schef/midi-organ/arduino/tests/deadcat/serial/74hc595-6/knight_rider_6.ino

//**************************************************************//
//  Name    : shiftOutCode, Hello World                                
//  Author  : Carlyn Maw,Tom Igoe, David A. Mellis 
//  Date    : 25 Oct, 2006    
//  Modified: 23 Mar 2010                                 
//  Version : 2.0                                             
//  Notes   : Code for using a 74HC595 Shift Register           //
//          : to count from 0 to 255                           
// http://arduino.cc/en/tutorial/ShiftOut
//****************************************************************

//Pin connected to ST_CP of 74HC595
int latchPin = 9; //SS
//Pin connected to SH_CP of 74HC595
int clockPin = 13; //SCK
////Pin connected to DS of 74HC595
int dataPin = 11; //MOSI

int oneByOne[8] = {1, 2, 4, 8, 16, 32, 64, 128};

int potPin = 5;    // select the input pin for the potentiometer

void setup() {
	//set pins to output so you can control the shift register
	pinMode(latchPin, OUTPUT);
	pinMode(clockPin, OUTPUT);
	pinMode(dataPin, OUTPUT);
}

int timer = 0;

void loop() {
	timer = analogRead(potPin);    // read the value from the sensor

	// count from 0 to 255 and display the number 
	// on the LEDs
	for (int i = 0; i < 8; i++) {
		// take the latchPin low so 
		// the LEDs don't change while you're sending in bits:
		digitalWrite(latchPin, LOW);
		// shift out the bits:
		shiftOut(dataPin, clockPin, MSBFIRST, 0);  
		shiftOut(dataPin, clockPin, MSBFIRST, 0);  
		shiftOut(dataPin, clockPin, MSBFIRST, 0);  
		shiftOut(dataPin, clockPin, MSBFIRST, 0);  
		shiftOut(dataPin, clockPin, MSBFIRST, 0);  
		shiftOut(dataPin, clockPin, MSBFIRST, oneByOne[i]);  

		//take the latch pin high so the LEDs will light up:
		digitalWrite(latchPin, HIGH);
		// pause before next value:
		timer = analogRead(potPin);    // read the value from the sensor
		delay(timer);
	}
	for (int i = 0; i < 8; i++) {
		// take the latchPin low so 
		// the LEDs don't change while you're sending in bits:
		digitalWrite(latchPin, LOW);
		// shift out the bits:
		shiftOut(dataPin, clockPin, MSBFIRST, 0);  
		shiftOut(dataPin, clockPin, MSBFIRST, 0);  
		shiftOut(dataPin, clockPin, MSBFIRST, 0);  
		shiftOut(dataPin, clockPin, MSBFIRST, 0);  
		shiftOut(dataPin, clockPin, MSBFIRST, oneByOne[i]);  
		shiftOut(dataPin, clockPin, MSBFIRST, 0);  

		//take the latch pin high so the LEDs will light up:
		digitalWrite(latchPin, HIGH);
		// pause before next value:
		timer = analogRead(potPin);    // read the value from the sensor
		delay(timer);
	}
	for (int i = 0; i < 8; i++) {
		// take the latchPin low so 
		// the LEDs don't change while you're sending in bits:
		digitalWrite(latchPin, LOW);
		// shift out the bits:
		shiftOut(dataPin, clockPin, MSBFIRST, 0);  
		shiftOut(dataPin, clockPin, MSBFIRST, 0);  
		shiftOut(dataPin, clockPin, MSBFIRST, 0);  
		shiftOut(dataPin, clockPin, MSBFIRST, oneByOne[i]);  
		shiftOut(dataPin, clockPin, MSBFIRST, 0);  
		shiftOut(dataPin, clockPin, MSBFIRST, 0);  

		//take the latch pin high so the LEDs will light up:
		digitalWrite(latchPin, HIGH);
		// pause before next value:
		timer = analogRead(potPin);    // read the value from the sensor
		delay(timer);
	}
	for (int i = 0; i < 8; i++) {
		// take the latchPin low so 
		// the LEDs don't change while you're sending in bits:
		digitalWrite(latchPin, LOW);
		// shift out the bits:
		shiftOut(dataPin, clockPin, MSBFIRST, 0);  
		shiftOut(dataPin, clockPin, MSBFIRST, 0);  
		shiftOut(dataPin, clockPin, MSBFIRST, oneByOne[i]);  
		shiftOut(dataPin, clockPin, MSBFIRST, 0);  
		shiftOut(dataPin, clockPin, MSBFIRST, 0);  
		shiftOut(dataPin, clockPin, MSBFIRST, 0);  

		//take the latch pin high so the LEDs will light up:
		digitalWrite(latchPin, HIGH);
		// pause before next value:
		timer = analogRead(potPin);    // read the value from the sensor
		delay(timer);
	}
	for (int i = 0; i < 8; i++) {
		// take the latchPin low so 
		// the LEDs don't change while you're sending in bits:
		digitalWrite(latchPin, LOW);
		// shift out the bits:
		shiftOut(dataPin, clockPin, MSBFIRST, 0);  
		shiftOut(dataPin, clockPin, MSBFIRST, oneByOne[i]);  
		shiftOut(dataPin, clockPin, MSBFIRST, 0);  
		shiftOut(dataPin, clockPin, MSBFIRST, 0);  
		shiftOut(dataPin, clockPin, MSBFIRST, 0);  
		shiftOut(dataPin, clockPin, MSBFIRST, 0);  

		//take the latch pin high so the LEDs will light up:
		digitalWrite(latchPin, HIGH);
		// pause before next value:
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
	shiftOut(dataPin, clockPin, MSBFIRST, 0);  
	shiftOut(dataPin, clockPin, MSBFIRST, 0);  
	shiftOut(dataPin, clockPin, MSBFIRST, 0);  
	shiftOut(dataPin, clockPin, MSBFIRST, 0);  
	digitalWrite(latchPin, HIGH);
	timer = analogRead(potPin);    // read the value from the sensor
	delay(timer*3);

}
