schef/midi-organ/arduino/tests/deadcat/midi-recive-60/src/sketch.ino

/*Receive MIDI and check if note = 60
By Amanda Ghassaei
July 2012
http://www.instructables.com/id/Send-and-Receive-MIDI-with-Arduino/

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
*/

byte commandByte;
byte noteByte;
byte velocityByte;

byte noteOn = 144;

//light up led at pin 13 when receiving noteON message with note = 60

void setup(){
  Serial.begin(31250);
  pinMode(13,OUTPUT);
  digitalWrite(13,LOW);
}

void checkMIDI(){
  do{
    if (Serial.available()){
      commandByte = Serial.read();//read first byte
      noteByte = Serial.read();//read next byte
      velocityByte = Serial.read();//read final byte
      if (commandByte == noteOn){//if note on message
        //check if note == 60 and velocity > 0
        if (noteByte == 60  && velocityByte > 0){
          digitalWrite(13,HIGH);//turn on led
        }
      }
    }
  }
  while (Serial.available() > 2);//when at least three bytes available
}
    

void loop(){
  checkMIDI();
  delay(100);
  digitalWrite(13,LOW);//turn led off
}
