schef/midi-organ/arduino/tests/deadcat/serial/serial_io/.build/atmega328/src/sketch.cpp

#include <Arduino.h>

void setup();
void loop();
#line 1 "src/sketch.ino"
/* Simple Serial ECHO script : Written by ScottC 03/07/2012 */

/* Use a variable called byteRead to temporarily store
   the data coming from the computer */
byte byteRead;

void setup() {                
// Turn the Serial Protocol ON
  Serial.begin(9600);
}

void loop() {
   /*  check if data has been sent from the computer: */
  if (Serial.available()) {
    /* read the most recent byte */
    byteRead = Serial.read();
    /*ECHO the value that was read, back to the serial port. */
    Serial.write(byteRead);
  }
}
