schef/midi-organ/arduino/tests/74hc164.ino

//Test example for 74hc164

#define data 4
#define clock 5

void setup()
{
  pinMode(clock, OUTPUT); // make the clock pin an output
  pinMode(data , OUTPUT); // make the data pin an output
  //shiftOut(data, clock, LSBFIRST, B10101010); // send this binary value to the shift register

 for(int i = 0; i < 8; ++i) //for 0 - 7 do
  {
    shiftOut(data, clock, MSBFIRST, 1 << i); // bit shift a logic high (1) value by i
    delay(100); // delay 100ms or you would not be able to see it
  }

}

void loop(){} // empty loop for now
